Renbrant/g29-load-cell-brake-controller/Photos/funcional prototipe/20260427_181801.jpg

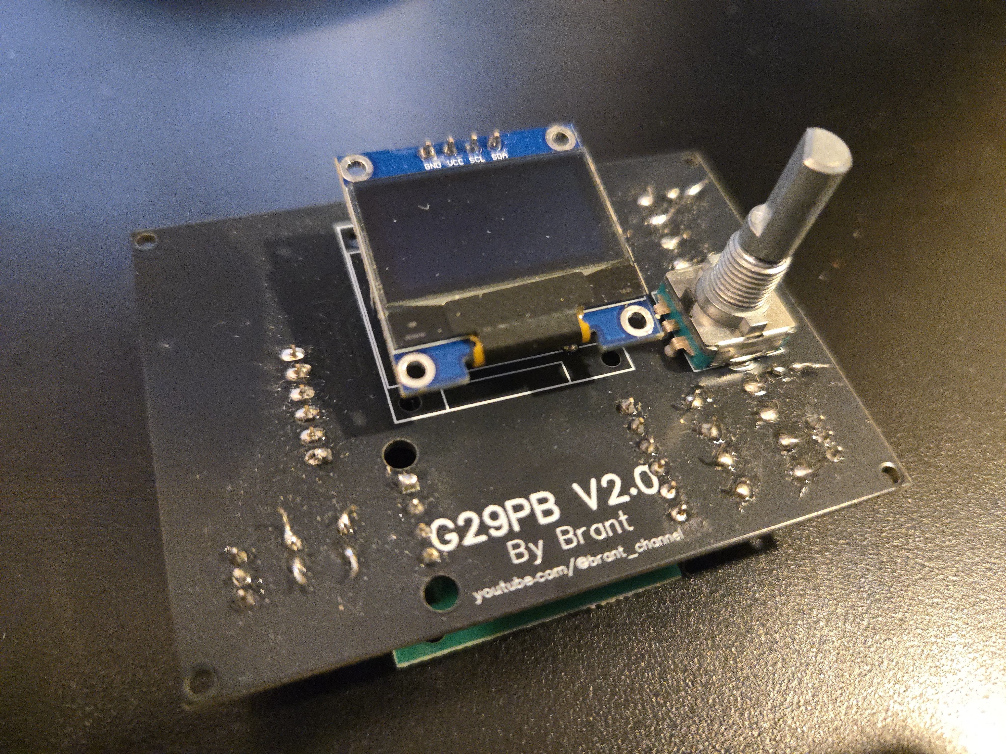
Photos/funcional prototipe/20260427_181801.jpg
