Renbrant/g29-load-cell-brake-controller/Photos/funcional prototipe/20260427_181812.jpg

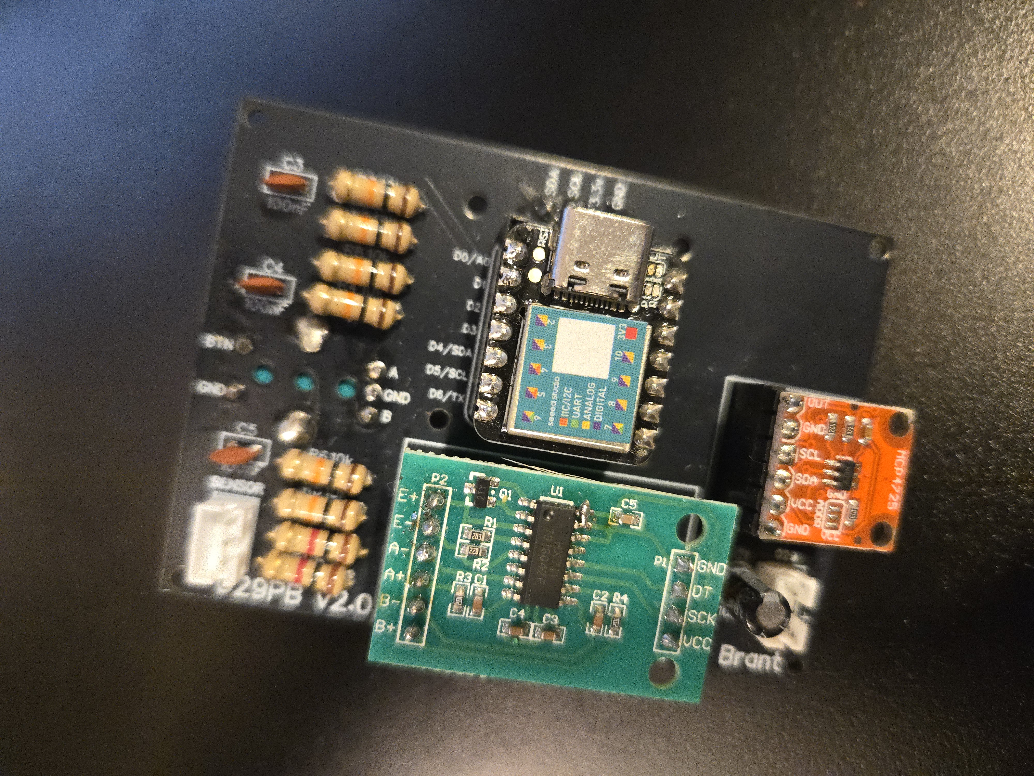
Photos/funcional prototipe/20260427_181812.jpg
